ifilot/p2000t-ram-expansion-board/img/ram_expansion_board_1056_03.jpg

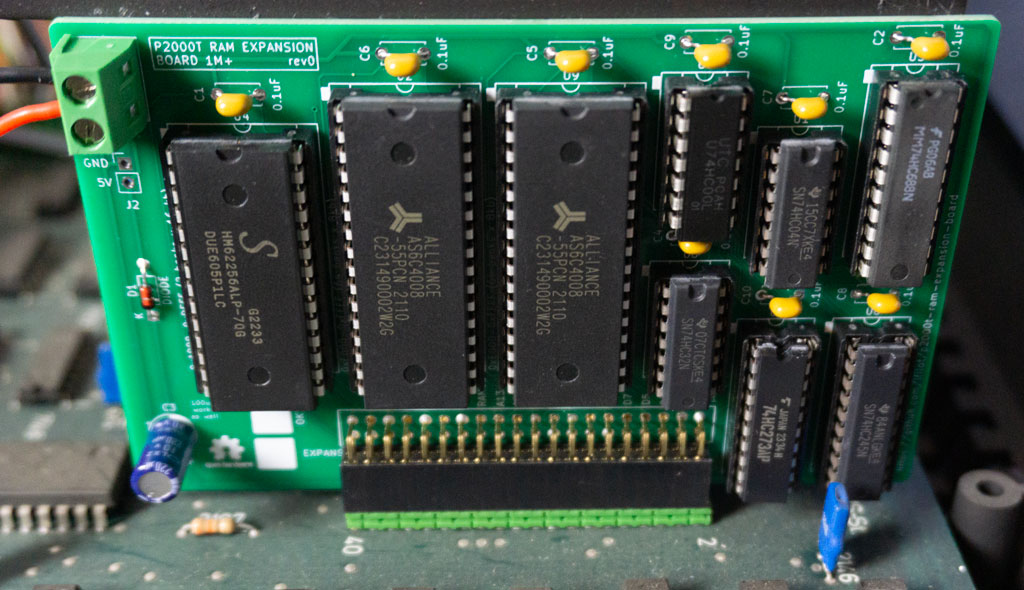
img/ram_expansion_board_1056_03.jpg
